tmiw/ezDV/firmware/main/network/icom/CIVState.cpp

/* 
 * This file is part of the ezDV project (https://github.com/tmiw/ezDV).
 * Copyright (c) 2022 Mooneer Salem
 * 
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
 * You should have received a copy of the GNU General Public License 
 * along with this program. If not, see <http://www.gnu.org/licenses/>.
 */

#include <functional>
#include "CIVState.h"
#include "IcomStateMachine.h"
#include "network/ReportingMessage.h"

namespace ezdv
{

namespace network
{

namespace icom
{

CIVState::CIVState(IcomStateMachine* parent)
    : TrackedPacketState(parent)
    , civWatchdogTimer_(parent_->getTask(), this, &CIVState::onCIVWatchdog_, MS_TO_US(WATCHDOG_PERIOD), "IcomCivWatchdog")
    , civSequenceNumber_(0)
    , civId_(0)
    , currentPttState_(false)
{
    parent_->getTask()->registerMessageHandler(this, &CIVState::onFreeDVSetPTTStateMessage_);
    parent_->getTask()->registerMessageHandler(this, &CIVState::onStopTransmitMessage_);
}

void CIVState::onEnterState()
{
    TrackedPacketState::onEnterState();
    
    // Initialize state
    civSequenceNumber_ = 0;
    civId_ = 0;
    
    sendCIVOpenPacket_();
    
    // Send request to get the radio ID on the other side.
    uint8_t civPacket[] = {
        0xFE,
        0xFE,
        0x00,
        0xE0,
        0x19, // Request radio ID command/subcommand
        0x00,
        0xFD
    };

    sendCIVPacket_(civPacket, sizeof(civPacket));
}

void CIVState::onExitState()
{
    civId_ = 0;
    
    civWatchdogTimer_.stop();

    // Send CIV close packet before performing general close processing.
    sendCIVClosePacket_();
    
    TrackedPacketState::onExitState();
}

std::string CIVState::getName()
{
    return "CIV";
}

void CIVState::onReceivePacket(IcomPacket& packet)
{
    uint8_t* civPacket;
    uint16_t civLength;
    
    if (packet.isCivPacket(&civPacket, &civLength))
    {
        civWatchdogTimer_.stop();
        
        ESP_LOGI(parent_->getName().c_str(), "Received CIV packet (from %02x, to %02x, type %02x)", civPacket[3], civPacket[2], civPacket[4]);
        
        // Get the current CI-V address of the radio for future use.
        if (civPacket[2] == 0xE0 && civPacket[4] == 0x19)
        {
            civId_ = civPacket[3];

            // Once we've retrieved the CIV ID, we should retrieve the current frequency
            // for Reporter support.
            uint8_t civPacket[] = {
                0xFE,
                0xFE,
                civId_,
                0xE0,
                0x03, // Request frequency
                0xFD
            };

            sendCIVPacket_(civPacket, sizeof(civPacket));
            
            // We should also reset the PTT state in case we lost connection during a state
            // change.
            ESP_LOGI(parent_->getName().c_str(), "Sending PTT CIV message (PTT = %d)", currentPttState_ ? 1 : 0);
        
            uint8_t civPttPacket[] = {
                0xFE,
                0xFE,
                civId_,
                0xE0,
                0x1C, // PTT on/off command/subcommand
                0x00,
                (uint8_t)(currentPttState_ ? 0x01 : 0x00), // enable PTT
                0xFD
            };
        
            sendCIVPacket_(civPttPacket, sizeof(civPttPacket));
        }
        else if (civPacket[3] == civId_)
        {
            if (civPacket[4] == 0x00 || civPacket[4] == 0x03)
            {
                // Get frequency data for future FreeDV Reporter support -- TBD
                // Frequency data is BCD and starts from index 5.
                uint64_t freqHz = 
                    (civPacket[5] & 0x0F) +                        // 1 Hz
                    ((civPacket[5] & 0xF0) >> 4) * 10           +  // 10 Hz
                    (civPacket[6] & 0x0F) * 100                 +  // 100 Hz
                    ((civPacket[6] & 0xF0) >> 4) * 1000         +  // 1 KHz
                    (civPacket[7] & 0x0F) * 10000               +  // 10 KHz
                    ((civPacket[7] & 0xF0) >> 4) * 100000       +  // 100 KHz
                    (civPacket[8] & 0x0F) * 1000000             +  // 1 MHz
                    ((civPacket[8] & 0xF0) >> 4) * 10000000     +  // 10 MHz
                    (civPacket[9] & 0x0F) * 100000000           +  // 100 MHz
                    ((civPacket[9] & 0xF0) >> 4) * 1000000000;     // 1 GHz

                ESP_LOGI(parent_->getName().c_str(), "Radio frequency changed to %" PRIu64 " Hz", freqHz);

                // Report frequency change to reporters
                ReportFrequencyChangeMessage message(freqHz);
                parent_->getTask()->publish(&message);
            }
        }
    }

    // Call into parent to perform missing packet handling.
    TrackedPacketState::onReceivePacket(packet);
}

void CIVState::onCIVWatchdog_(DVTimer*)
{
    ESP_LOGW(parent_->getName().c_str(), "No CIV data received recently, reconnecting channel");
    parent_->transitionState(IcomProtocolState::ARE_YOU_THERE);
}

void CIVState::sendCIVOpenPacket_()
{
    ESP_LOGI(parent_->getName().c_str(), "Sending CIV open packet");
    auto packet = IcomPacket::CreateCIVOpenClosePacket(civSequenceNumber_++, parent_->getOurIdentifier(), parent_->getTheirIdentifier(), false);
    sendTracked_(packet);
}

void CIVState::sendCIVClosePacket_()
{
    ESP_LOGI(parent_->getName().c_str(), "Sending CIV close packet");
    auto packet = IcomPacket::CreateCIVOpenClosePacket(civSequenceNumber_++, parent_->getOurIdentifier(), parent_->getTheirIdentifier(), true);
    sendTracked_(packet);
}

void CIVState::sendCIVPacket_(uint8_t* civPacket, uint16_t civLength)
{
    ESP_LOGI(parent_->getName().c_str(), "Sending CIV data packet");
    auto packet = IcomPacket::CreateCIVPacket(parent_->getOurIdentifier(), parent_->getTheirIdentifier(), civSequenceNumber_++, civPacket, civLength);
    sendTracked_(packet);
    
    civWatchdogTimer_.stop();
    civWatchdogTimer_.start();
}

void CIVState::onFreeDVSetPTTStateMessage_(DVTask* origin, ezdv::audio::FreeDVSetPTTStateMessage* message)
{
    if (civId_ > 0 && message->pttState)
    {
        // This only handles the beginning of TX. Ending TX is handled by TransmitCompleteMessage.
        ESP_LOGI(parent_->getName().c_str(), "Sending PTT CIV message (PTT = %d)", message->pttState);
        
        uint8_t civPacket[] = {
            0xFE,
            0xFE,
            civId_,
            0xE0,
            0x1C, // PTT on/off command/subcommand
            0x00,
            (uint8_t)0x01, // enable PTT
            0xFD
        };
        
        sendCIVPacket_(civPacket, sizeof(civPacket));
        
        currentPttState_ = true;
    }
}

void CIVState::onStopTransmitMessage_(DVTask* origin, StopTransmitMessage* message)
{
    if (civId_ > 0)
    {
        ESP_LOGI(parent_->getName().c_str(), "Sending PTT CIV message (PTT = %d)", 0);
        
        uint8_t civPacket[] = {
            0xFE,
            0xFE,
            civId_,
            0xE0,
            0x1C, // PTT on/off command/subcommand
            0x00,
            (uint8_t)0x00, // disable PTT
            0xFD
        };
        
        sendCIVPacket_(civPacket, sizeof(civPacket));
        
        currentPttState_ = false;
    }
}

}

}

}
