tmiw/ezDV/firmware/main/driver/TLV320.cpp

/* 
 * This file is part of the ezDV project (https://github.com/tmiw/ezDV).
 * Copyright (c) 2022 Mooneer Salem
 * 
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
 * You should have received a copy of the GNU General Public License 
 * along with this program. If not, see <http://www.gnu.org/licenses/>.
 */

#include <cstring>

#include "esp_log.h"
#include "driver/gpio.h"
#include "driver/i2s_std.h"

#include "TLV320.h"
#include "TLV320Message.h"

// TLV320 reset pin GPIO
#define TLV320_RESET_GPIO GPIO_NUM_13

// TLV320 I2S interface GPIOs
#define TLV320_MCLK_GPIO GPIO_NUM_3
#define TLV320_BCLK_GPIO GPIO_NUM_46
#define TLV320_WCLK_GPIO GPIO_NUM_9
#define TLV320_DIN_GPIO GPIO_NUM_11
#define TLV320_DOUT_GPIO GPIO_NUM_10

// TLV320 I2C address
#define TLV320_I2C_ADDRESS (0x18)

// Tag to prepend to log entries coming from this file.
#define CURRENT_LOG_TAG ("TLV320Driver")

// Timer constants below are for 8000 Hz sample rate
#define I2S_NUM_SAMPLES_PER_INTERVAL (160)

namespace ezdv
{

namespace driver
{

using namespace std::placeholders;

TLV320::TLV320(I2CMaster* i2cMaster)
    : DVTask("TLV320Driver", 15, 4096, tskNO_AFFINITY, 10, pdMS_TO_TICKS(10))
    , audio::AudioInput(2, 2)
    , currentPage_(-1) // This will cause the page to be set to 0 on first I2C write.
    , i2sTxDevice_(nullptr)
    , i2sRxDevice_(nullptr)
    , int1Gpio_(this, std::bind(&TLV320::onInterrupt1Fire_, this, _2), false, true, false)
    , int2Gpio_(this, std::bind(&TLV320::onInterrupt2Fire_, this, _2), false, true, false)
{
    // Register message handlers
    registerMessageHandler<storage::LeftChannelVolumeMessage>(this, &TLV320::onLeftChannelVolume_);
    registerMessageHandler<storage::RightChannelVolumeMessage>(this, &TLV320::onRightChannelVolume_);

    initializeResetGPIO_();
    
    i2cDevice_ = i2cMaster->getDevice(TLV320_I2C_ADDRESS);
    assert(i2cDevice_ != nullptr);
}

TLV320::~TLV320()
{
    delete i2cDevice_;
}

void TLV320::onTaskStart_()
{
    // To begin, we need to hard reset the TLV320.
    ESP_LOGI(CURRENT_LOG_TAG, "reset TLV320");
    initializeResetGPIO_();
    tlv320HardReset_();
    
    // Make sure the TLV320 is actually there. If not, no point in continuing.
    bool result = false;
    getConfigurationOption_(0, 0, &result);
    if (!result)
    {
        ESP_LOGW(CURRENT_LOG_TAG, "Cannot communicate with TLV320, possibly using ezDV on board without one");
        return;
    }
    
    // Initialize I2S.
    initializeI2S_();
    
    // Enable required clocks.
    ESP_LOGI(CURRENT_LOG_TAG, "configure clocks");
    tlv320ConfigureClocks_();
    
    // Configure processing blocks
    ESP_LOGI(CURRENT_LOG_TAG, "configure processing blocks");
    tlv320ConfigureProcessingBlocks_();
    
    ESP_LOGI(CURRENT_LOG_TAG, "configure LDOs");
    tlv320ConfigurePower_();
    
    // Set power and I/O routing (ADC).
    ESP_LOGI(CURRENT_LOG_TAG, "configure routing for ADC");
    tlv320ConfigureRoutingADC_();
    
    // Set power and I/O routing (DAC).
    ESP_LOGI(CURRENT_LOG_TAG, "configure routing for DAC");
    tlv320ConfigureRoutingDAC_();

    // Enable interrupts
    ESP_LOGI(CURRENT_LOG_TAG, "configuring interrupts");
    tlv320ConfigureInterrupts_();

    // Note: restoring AGC volumes is delayed until we get the power-on
    // volumes from storage.
    ESP_LOGI(CURRENT_LOG_TAG, "all audio codec config complete");
}

void TLV320::onTaskSleep_()
{
    // Stop reading from I2S.
    if (i2sRxDevice_ != nullptr)
    {
        i2s_channel_disable(i2sRxDevice_);
        i2s_del_channel(i2sRxDevice_);
    }
    
    if (i2sTxDevice_ != nullptr)
    {
        i2s_channel_disable(i2sTxDevice_);
        i2s_del_channel(i2sTxDevice_);
    }
    
    i2sRxDevice_ = nullptr;
    i2sTxDevice_ = nullptr;

    tlv320HardReset_();
}

void TLV320::onTaskTick_()
{
    if (i2sRxDevice_ == nullptr || i2sTxDevice_ == nullptr) return;

    short tempData[I2S_NUM_SAMPLES_PER_INTERVAL * 2];
    memset(tempData, 0, sizeof(tempData));
    
    // Perform read from I2S. 
    size_t bytesRead = sizeof(tempData);
    ESP_ERROR_CHECK(i2s_channel_read(i2sRxDevice_, tempData, sizeof(tempData), &bytesRead, portMAX_DELAY));

    // Output channel bytes to configured output FIFOs.
    struct FIFO* leftChannelFifo = getAudioOutput(audio::AudioInput::ChannelLabel::LEFT_CHANNEL);
    struct FIFO* rightChannelFifo = getAudioOutput(audio::AudioInput::ChannelLabel::RIGHT_CHANNEL);
    for (int index = 0; index < bytesRead / 2 / sizeof(short); index++)
    {
        if (leftChannelFifo != nullptr) codec2_fifo_write(leftChannelFifo, &tempData[2*index], 1);
        if (rightChannelFifo != nullptr) codec2_fifo_write(rightChannelFifo, &tempData[2*index + 1], 1);
    }

    leftChannelFifo = getAudioInput(audio::AudioInput::ChannelLabel::LEFT_CHANNEL);
    rightChannelFifo = getAudioInput(audio::AudioInput::ChannelLabel::RIGHT_CHANNEL);
    if ((leftChannelFifo && codec2_fifo_used(leftChannelFifo) >= I2S_NUM_SAMPLES_PER_INTERVAL) || 
        (rightChannelFifo && codec2_fifo_used(rightChannelFifo) >= I2S_NUM_SAMPLES_PER_INTERVAL))
    {
        memset(tempData, 0, sizeof(tempData));
        
        for (auto index = 0; index < I2S_NUM_SAMPLES_PER_INTERVAL; index++)
        {
            if (leftChannelFifo) codec2_fifo_read(leftChannelFifo, &tempData[2*index], 1);
            if (rightChannelFifo) codec2_fifo_read(rightChannelFifo, &tempData[2*index + 1], 1);
        }
        
        size_t bytesWritten = 0;
        ESP_ERROR_CHECK(i2s_channel_write(i2sTxDevice_, tempData, sizeof(tempData), &bytesWritten, portMAX_DELAY));
    }
}

void TLV320::setVolumeCommon_(uint8_t reg, int8_t vol)
{
    ESP_LOGI(CURRENT_LOG_TAG, "Volume control: setting volume on register %d to %d", (int)reg, vol);    
    setConfigurationOption_(0, reg, vol);
}

void TLV320::onLeftChannelVolume_(DVTask* origin, storage::LeftChannelVolumeMessage* message)
{
    setVolumeCommon_(65, message->volume);
}

void TLV320::onRightChannelVolume_(DVTask* origin, storage::RightChannelVolumeMessage* message)
{
    setVolumeCommon_(66, message->volume);
}

void TLV320::setPage_(uint8_t page)
{
    uint8_t buf[] = { page };
    i2cDevice_->writeBytes(0, buf, sizeof(buf));
    currentPage_ = page;
}

void TLV320::setConfigurationOption_(uint8_t page, uint8_t reg, uint8_t val)
{
    if (page != currentPage_)
    {
        setPage_(page);
    }
    
    uint8_t buf[] = { val };
    i2cDevice_->writeBytes(reg, buf, sizeof(buf));
}

void TLV320::setConfigurationOptionMultiple_(uint8_t page, uint8_t reg, uint8_t* val, uint8_t size)
{
    if (page != currentPage_)
    {
        setPage_(page);
    }

    i2cDevice_->writeBytes(reg, val, size);
}

uint8_t TLV320::getConfigurationOption_(uint8_t page, uint8_t reg, bool* readResult)
{
    if (page != currentPage_)
    {
        setPage_(page);
    }
    
    uint8_t result[] = { 0 };
    auto rv = i2cDevice_->readBytes(reg, result, sizeof(result));
    if (!rv)
    {
        ESP_LOGE(CURRENT_LOG_TAG, "Could not read bytes from I2C!");
    }
    
    if (readResult != nullptr)
    {
        *readResult = rv;
    }
    
    return result[0];
}

void TLV320::initializeI2S_()
{
    // Get the default channel configuration by helper macro.
    i2s_chan_config_t chan_cfg = I2S_CHANNEL_DEFAULT_CONFIG(I2S_NUM_0, I2S_ROLE_MASTER);

    // Update DMA info for the channel to prevent overflows.
    //chan_cfg.dma_desc_num = 16;
    //chan_cfg.dma_frame_num = I2S_NUM_SAMPLES_PER_INTERVAL;
    chan_cfg.auto_clear = true;
    
    // Allocate a new full duplex channel and get the handles of the channels
    ESP_ERROR_CHECK(i2s_new_channel(&chan_cfg, &i2sTxDevice_, &i2sRxDevice_));

    // Set up configuration for the I2S device:
    //     8 KHz sample rate
    //     Philips format (1 bit shifted, 16 bit/channel stereo)
    //     GPIOs as listed
    i2s_std_config_t i2sConfiguration = {
        .clk_cfg = {
            .sample_rate_hz = 8000,
            .clk_src = I2S_CLK_SRC_DEFAULT,
            .ext_clk_freq_hz = 0, // ignored by ESP-IDF
            .mclk_multiple = I2S_MCLK_MULTIPLE_256,
        },
        .slot_cfg = I2S_STD_PHILIP_SLOT_DEFAULT_CONFIG(I2S_DATA_BIT_WIDTH_16BIT, I2S_SLOT_MODE_STEREO),
        .gpio_cfg = {
            .mclk = TLV320_MCLK_GPIO,
            .bclk = TLV320_BCLK_GPIO,
            .ws = TLV320_WCLK_GPIO,
            .dout = TLV320_DOUT_GPIO,
            .din = TLV320_DIN_GPIO,
            .invert_flags = {
                .mclk_inv = false,
                .bclk_inv = false,
                .ws_inv = false,
            },
        },
    };
    
    // Set clock multiplier to 512 to support increased DAC oversampling ratio
    i2sConfiguration.clk_cfg.mclk_multiple = I2S_MCLK_MULTIPLE_512;

    ESP_ERROR_CHECK(i2s_channel_init_std_mode(i2sTxDevice_, &i2sConfiguration));
    ESP_ERROR_CHECK(i2s_channel_init_std_mode(i2sRxDevice_, &i2sConfiguration));
    ESP_ERROR_CHECK(i2s_channel_enable(i2sTxDevice_));
    ESP_ERROR_CHECK(i2s_channel_enable(i2sRxDevice_));
}

void TLV320::initializeResetGPIO_()
{
    gpio_intr_disable(TLV320_RESET_GPIO);
    gpio_set_direction(TLV320_RESET_GPIO, GPIO_MODE_OUTPUT);
    gpio_set_pull_mode(TLV320_RESET_GPIO, GPIO_FLOATING);
    gpio_set_level(TLV320_RESET_GPIO, 1); // active low
}

void TLV320::tlv320HardReset_()
{
    // TLV320's reset line must be held low for 10ns for the reset
    // to start. We also have to wait for 1ms after the reset
    // goes high for everything to reset properly. See section 3.1-3.2 
    // of the Application Reference Guide 
    // (https://www.ti.com/lit/an/slaa408a/slaa408a.pdf).
    gpio_set_level(TLV320_RESET_GPIO, 0);
    esp_rom_delay_us(1);
    gpio_set_level(TLV320_RESET_GPIO, 1);
    vTaskDelay(pdMS_TO_TICKS(1));
}

void TLV320::tlv320ConfigureClocks_()
{
    // Clock calculations for 8K sample rate per guide at 
    // https://www.ti.com/lit/an/slaa404c/slaa404c.pdf
            
    // AOSR = 128
    // DOSR = 768
    // ADC_FS = 8K
    // DAC_FS = 8K
    // ADC_MOD_CLK = AOSR * ADC_FS = 128 * 8000 = 1.024 MHz <= 6.758 MHz
    // DAC_MOD_CLK = DOSR * DAC_FS = 768 * 8000 = 6.144 MHz <= 6.758 MHz
    
    // ADC Processing Block = PRB_R1
    // DAC Processing Block = PRB_P1
    // MADC = 48
    // MDAC = 8
    // ADC_CLK = MADC * ADC_MOD_CLK = 48 * 1.024 MHz = 49.152 MHz
    // DAC_CLK = MDAC * DAC_MOD_CLK = 8 * 6.144 MHz = 49.152 MHz
    // (MADC * AOSR) / 32 = 6144 / 32 = 192 >= RC(R1) = 6
    // (MDAC * DOSR) / 32 = 6144 / 32 = 192 >= RC(P1) = 8
    // ADC_CLK <= 55.296 MHz
    // DAC_CLK <= 55.296 MHz
    
    // NADC = 2
    // NDAC = 2
    // CODEC_CLKIN = NADC * ADC_CLK = NDAC * DAC_CLK = 98.304 MHz
    // CODEC_CLKIN <= 137MHz
    // CODEC_CLKIN from PLL_CLK
    
    // PLL_CLK = MCLK * R * J.D/P
    // 98.304 MHz = 4.096 * 1 * 24.0000 / 1
    // P = 1, R = 1, J = 24, D = 0 

    uint8_t pllOpts[] = {
        // Set CODEC_CLKIN to PLL and use MCLK for PLL
        // (Page 0, register 4)
        (0 << 2) | 0b11,

        // Set PLL P = 1, R = 1, J = 24, D = 0, power up PLL
        // (Page 0, registers 5-8)
        (1 << 7) | (0b001 << 4) | (0b001),  // P, R, power up
        24, // J
        0, // D[MSB]
        0 // D[LSB]
    };
    setConfigurationOptionMultiple_(0, 4, pllOpts, 5);

    // Wait 10ms for PLL to become available
    // (Section 2.7.1, "TLV320AIC3254 Application Reference Guide")
    vTaskDelay(pdMS_TO_TICKS(10));
        
    // Set NDAC = 2, MDAC = 8. Power on divider.
    // (Page 0, registers 11 and 12)
    // Program DOSR to 768 (Page 0, registers 13-14)
    uint8_t dacOpts[] = {
        (1 << 7) | 2,
        (1 << 7) | 8,
        0b11,
        0
    };
    setConfigurationOptionMultiple_(0, 11, dacOpts, 4);
        
    // Set NADC = 2, MADC = 48. (Page 0, registers 18 and 19)
    // Program AOSR to 128 (Page 0, register 20).
    uint8_t adcOpts[] = {
        2,
        (1 << 7) | 48,
        128
    };
    setConfigurationOptionMultiple_(0, 18, adcOpts, 2);
    
    // Set I2S word size to 16 bits (Page 0, register 27)
    setConfigurationOption_(0, 27, 0);
    
#if 0
    // Loopback audio at the ADC/DAC level
    setConfigurationOption_(0, 29, 1 << 4);
#endif // 0
}

void TLV320::tlv320ConfigurePower_()
{
    // Power up AVDD LDO
    setConfigurationOption_(1, 2, (1 << 3) | (1 << 0));
    
    // Disable weak AVDD in presence of external AVDD supply (Page 1, register 1)
    setConfigurationOption_(1, 1, (1 << 3));
    
    // AVDD/DVDD 1.72V, AVDD LDO powered up (Page 1, register 2)
    setConfigurationOption_(1, 2, (0 << 3) | (1 << 0));
    
    // Set full chip common mode to 0.9V
    // HP output CM = 1.65V
    // HP driver supply = LDOin voltage
    // Line output CM = 1.65V
    // Line output supply = LDOin voltage
    // (Page 1, register 10)
    setConfigurationOption_(1, 10, (3 << 4) | (1 << 3) | (1 << 1) | (1 << 0));
    
    // Set ADC PTM to PTM_R1 (Page 1, register 61)
    setConfigurationOption_(1, 61, 0xFF);
    
    // Set DAC PTM to PTM_P1 (Page 1, registers 3-4)
    // Note: PTM_P4 requires >= 20 bits for I2S, hence not used here.
    uint8_t dacPtm[] = {
        0x2 << 2,
        0x2 << 2
    };
    setConfigurationOptionMultiple_(1, 3, dacPtm, 2);
    
    // Set input powerup time to 3.1ms (Page 1, register 71)
    setConfigurationOption_(1, 71, 0b110001);
    
    // REF will power up in 40ms (Page 1, register 123)
    setConfigurationOption_(1, 123, 1);
}

void TLV320::tlv320ConfigureProcessingBlocks_()
{
    // Set ADC_PRB and DAC_PRB to P1 and R1 (Page 0, registers 60-61).
    // Note: Use ADC_PRB = R2 if enabling the ADC filter below.
    uint8_t prb[] = {
        1,
        1
    };
    setConfigurationOptionMultiple_(0, 60, prb, 2);
    
    // Set ADC filter coefficients for HPF, center frequency 130 Hz.
    // All five biquads on both channels are set to this filter to reduce
    // background hiss in the recorded audio.
    uint8_t adcFilter[] = {
        0x77, 0x15, 0x39, 0x00,
        0x88, 0xEA, 0xC7, 0x00,
        0x77, 0x15, 0x39, 0x00,
        0x76, 0xC5, 0xA2, 0x00,
        0x91, 0x36, 0x60, 0x00
    };
    setConfigurationOptionMultiple_(8, 36, adcFilter, sizeof(adcFilter));
    setConfigurationOptionMultiple_(9, 44, adcFilter, sizeof(adcFilter));
    setConfigurationOptionMultiple_(8, 56, adcFilter, sizeof(adcFilter));
    setConfigurationOptionMultiple_(9, 64, adcFilter, sizeof(adcFilter));
    setConfigurationOptionMultiple_(8, 76, adcFilter, sizeof(adcFilter));
    setConfigurationOptionMultiple_(9, 84, adcFilter, sizeof(adcFilter));
    setConfigurationOptionMultiple_(8, 96, adcFilter, sizeof(adcFilter));
    setConfigurationOptionMultiple_(9, 104, adcFilter, sizeof(adcFilter));
    setConfigurationOptionMultiple_(8, 116, adcFilter, sizeof(adcFilter));
    setConfigurationOptionMultiple_(9, 124, adcFilter, sizeof(adcFilter));
}

void TLV320::tlv320ConfigureRoutingADC_()
{
    // Enable 2.5V mic bias on headset jack using LDOIN (Page 1, register 51)
    setConfigurationOption_(1, 51, (1 << 6) | (0b10 << 4) | (1 << 3));
    
    // Set ADC routing: IN1_L left channel, IN1_R right channel,
    // 20kohm impedence (Page 1, registers 52, 54, 55, 57)
    setConfigurationOption_(1, 52, 0b10 << 6);
    setConfigurationOption_(1, 54, 0b10 << 6);
    setConfigurationOption_(1, 55, 0b10 << 6);
    setConfigurationOption_(1, 57, 0b10 << 6);
    
    // Weakly connect all unused inputs to ground.
    // (Page 1, register 58)
    setConfigurationOption_(1, 58, (1 << 5) | (1 << 4) | (1 << 3) | (1 << 2));
    
    // Unmute PGAs, gain = 6dB due to 20k impedence
    // (Page 1, registers 59 and 60)
    setConfigurationOption_(1, 59, 0x0c);
    setConfigurationOption_(1, 60, 0x0c);
    
    // Power on ADC (Page 0, register 81)
    setConfigurationOption_(0, 81, (1 << 7) | (1 << 6));
    
    // Unmute ADC (Page 0, register 82)
    setConfigurationOption_(0, 82, 0);
    
    //setConfigurationOption_(0, 84, 0b0101000 /*0x0c*/);
    
    tlv320ConfigureAGC_();
}

void TLV320::tlv320ConfigureRoutingDAC_()
{
    // 6kohm depop, N = 6.0 (Page 1, register 20)
    setConfigurationOption_(1, 20, (0b1010 << 2) | (0b01 << 0));
    
    // Set DAC routing: HPL, HPR come from DAC
    // (Page 1, registers 12 and 13)
    setConfigurationOption_(1, 12, 1 << 3);
    setConfigurationOption_(1, 13, 1 << 3);
    
    // Unmute HPL and HPR, gain = 0dB
    // (Page 1, registers 16 and 17)
    setConfigurationOption_(1, 16, 0);
    setConfigurationOption_(1, 17, 0);

    // Power up HPL and HPR
    // (Page 1, register 9)
    setConfigurationOption_(1, 9, (1 << 5) | (1 << 4));
    
    // Wait until gain fully applied. This effectively takes ~2.5s
    // to complete unless the TLV320 gets back to us sooner.
    // (Page 1, register 63)
    uint8_t gainRegVal = 0;
    int count = 0;
    do
    {
        vTaskDelay(pdMS_TO_TICKS(10));
        gainRegVal = getConfigurationOption_(1, 63);
    } while ((count++ <= 250) && (gainRegVal & (0b11 << 6)) == 0);

    if (count > 250)
    {
        ESP_LOGW(CURRENT_LOG_TAG, "Timed out waiting for gain to fully apply, assuming it's already taken effect");
    }
    
    // Power on DAC (Page 0, register 63)
    setConfigurationOption_(0, 63, (1 << 7) | (1 << 6) | (1 << 4) | (1 << 2) | (1 << 1));
    
    // Unmute DAC (Page 0, register 64)
    setConfigurationOption_(0, 64, 0);
}

void TLV320::tlv320ConfigureAGC_()
{
    uint8_t agcConfig[] = {
        // Enable AGC, -16dB target, gain hysteresis disabled
        (1 << 7) | (0b101 << 4) | (0b00 << 0),  
        
        // Hysteresis 2dB, -90dB noise threshold
        (0b01 << 6) | (0b11111 << 1),
        
        // 40dB maximum gain
        0x50, //0b100100,
        
        // Attack time = 20ms (25 * 32 clocks, scale 2)
        0x08,
        
        // Decay time = 500ms (19 * 512 clocks, scale 2)
        0x32,
        
        // Noise debounce = 0ms
        0x00,
        
        // Signal debounce = 2ms
        0x06,
    };
    
    // Set AGC configuration for both channels (page 0, register 86 for left, register 94 for right)
    setConfigurationOptionMultiple_(0, 86, agcConfig, sizeof(agcConfig));
    setConfigurationOptionMultiple_(0, 94, agcConfig, sizeof(agcConfig));
}

void TLV320::tlv320ConfigureInterrupts_()
{
    // Set headphone overcurrent detection debounce to 128ms
    // (Page 1, Register 11, Bit D4 = 1, D3-1 = 101)
    setConfigurationOption_(1, 11, (1 << 4) | (0b101 << 1));
    
    // Use INT1 for ADC/DAC overload event
    // (Page 0, Register 48, Bit D2 = 1)

    // Use INT2 for button press, headset detect event
    // (Page 0, Register 49, Bit D6 = 1)

    uint8_t interruptConfig[] = 
    {
        (1 << 2) | (1 << 0),
        (1 << 7) | (1 << 6) | (1 << 0)
    };
    setConfigurationOptionMultiple_(0, 48, interruptConfig, sizeof(interruptConfig));

    // Disable SCLK so we can use it for headset detection
    // (Page 0, Register 56, D2-D1 = 00)
    setConfigurationOption_(0, 56, 0b00 << 1);

    // Enable headset detection (required for button detection) with 32ms debounce.
    // (Page 0, Register 67, D7 = 1)
    setConfigurationOption_(0, 67, (1 << 7) | (0b11 << 0));

    // INT1 output on MFP4
    // (Page 0, Register 55, Bits D4-D1 = 0100)
    setConfigurationOption_(0, 55, 0b0100 << 1);

    // INT2 output on MFP5
    // (Page 0, Register 52, Bits D5-D2 = 0110)
    setConfigurationOption_(0, 52, 0b0110 << 2);

    // Enable interrupts
    int1Gpio_.start();
    int1Gpio_.enableInterrupt(true);
    int2Gpio_.start();
    int2Gpio_.enableInterrupt(true);
}

void TLV320::onInterrupt1Fire_(bool state)
{
    // Page 0, register 42, bits D3-D2 contain the ADC channels that
    // overloaded.
    auto val = getConfigurationOption_(0, 42);
    bool leftAdcOverload = val & (1 << 3);
    bool rightAdcOverload = val & (1 << 2);

    if (state && (leftAdcOverload || rightAdcOverload))
    {
        ESP_LOGW(CURRENT_LOG_TAG, "ADC overload! (Left/User = %d, Right/Radio = %d)", leftAdcOverload, rightAdcOverload);

        // Broadcast current ADC status to interested parties.
        OverloadStateMessage message(leftAdcOverload, rightAdcOverload);
        publish(&message);
    }
    else
    {
        // Broadcast "clear" ADC message so that any indication (LED, etc.)
        // doesn't remain.
        OverloadStateMessage message(false, false);
        publish(&message);
    }
}

void TLV320::onInterrupt2Fire_(bool state)
{   
    if (state)
    {
        // Page 0, register 44, bit D5 contains the status of the headset button
        auto val = getConfigurationOption_(0, 44);
        ESP_LOGI(CURRENT_LOG_TAG, "button state: %x", val);
        if (val & (1 << 5))
        {
            ESP_LOGI(CURRENT_LOG_TAG, "Headset button pressed");

            HeadsetButtonPressMessage message;
            publish(&message);
        }
    }
}

} // namespace driver

} // namespace ezdv
