tmiw/ezDV/firmware/main/driver/ButtonArray.cpp

/* 
 * This file is part of the ezDV project (https://github.com/tmiw/ezDV).
 * Copyright (c) 2022 Mooneer Salem
 * 
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
 * You should have received a copy of the GNU General Public License 
 * along with this program. If not, see <http://www.gnu.org/licenses/>.
 */

#include "esp_log.h"

#include "ButtonArray.h"
#include "InputGPIO.h"

// One second for long press
#define LONG_PRESS_INTERVAL_US (1000000)

namespace ezdv
{

namespace driver
{

using namespace std::placeholders;

ButtonArray::ButtonArray()
    : DVTask("ButtonArray", 10, 3072, tskNO_AFFINITY, 10)
    , pttButtonTimer_(this, std::bind(&ButtonArray::handleLongPressButton_, this, ButtonLabel::PTT), LONG_PRESS_INTERVAL_US, "PttButtonTimer")
    , modeButtonTimer_(this, std::bind(&ButtonArray::handleLongPressButton_, this, ButtonLabel::MODE), LONG_PRESS_INTERVAL_US, "ModeButtonTimer")
    , volUpButtonTimer_(this, std::bind(&ButtonArray::handleLongPressButton_, this, ButtonLabel::VOL_UP), LONG_PRESS_INTERVAL_US, "VolUpTimer")
    , volDownButtonTimer_(this, std::bind(&ButtonArray::handleLongPressButton_, this, ButtonLabel::VOL_DOWN), LONG_PRESS_INTERVAL_US, "VolDownTimer")
    , pttButton_(this, std::bind(&ButtonArray::handleButton_, this, ButtonLabel::PTT, _2))
    , modeButton_(this, std::bind(&ButtonArray::handleButton_, this, ButtonLabel::MODE, _2))
    , volUpButton_(this, std::bind(&ButtonArray::handleButton_, this, ButtonLabel::VOL_UP, _2))
    , volDownButton_(this, std::bind(&ButtonArray::handleButton_, this, ButtonLabel::VOL_DOWN, _2))
{
    // empty
}

ButtonArray::~ButtonArray()
{
    // empty
}

void ButtonArray::onTaskStart_()
{
    pttButton_.start();
    pttButton_.enableInterrupt(true);
    
    modeButton_.start();
    modeButton_.enableInterrupt(true);
    
    volUpButton_.start();
    volUpButton_.enableInterrupt(true);
    
    volDownButton_.start();
    volDownButton_.enableInterrupt(true);
}

void ButtonArray::onTaskSleep_()
{
    pttButton_.enableInterrupt(false);
    modeButton_.enableInterrupt(false);
    volUpButton_.enableInterrupt(false);
    volDownButton_.enableInterrupt(false);
}

static const char* ButtonLabelStrings_[] = {
    "None",
    "PTT",
    "Mode",
    "VolUp",
    "VolDown"
};

void ButtonArray::handleButton_(ButtonLabel label, bool val)
{
    DVTimer* timerToSet = nullptr;
    bool buttonPressed = !val;

    switch(label)
    {
        case ButtonLabel::PTT:
            timerToSet = &pttButtonTimer_;
            break;
        case ButtonLabel::MODE:
            timerToSet = &modeButtonTimer_;
            break;
        case ButtonLabel::VOL_UP:
            timerToSet = &volUpButtonTimer_;
            break;
        case ButtonLabel::VOL_DOWN:
            timerToSet = &volDownButtonTimer_;
            break;
        default:
            assert(0);
    }

    ESP_LOGI("ButtonArray", "Button %s now %d", ButtonLabelStrings_[label], (int)buttonPressed);

    // Start long press timer
    if (buttonPressed)
    {
        ButtonShortPressedMessage* message = new ButtonShortPressedMessage(label);
        publish(message);
        delete message;

        if (timerToSet != nullptr)
        {
            timerToSet->stop();
            timerToSet->start(true);
        }
    }
    else
    {
        if (timerToSet != nullptr)
        {
            timerToSet->stop();
        }
        
        ButtonReleasedMessage* message = new ButtonReleasedMessage(label);
        publish(message);
        delete message;
    }
}

void ButtonArray::handleLongPressButton_(ButtonLabel label)
{
    ESP_LOGI("ButtonArray", "Button %s long pressed", ButtonLabelStrings_[label]);

    ButtonLongPressedMessage* message = new ButtonLongPressedMessage(label);
    publish(message);
    delete message;
}

}

}
