tmiw/ezDV/firmware/main/network/icom/IcomMessage.h

/* 
 * This file is part of the ezDV project (https://github.com/tmiw/ezDV).
 * Copyright (c) 2022 Mooneer Salem
 * 
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
 * You should have received a copy of the GNU General Public License 
 * along with this program. If not, see <http://www.gnu.org/licenses/>.
 */

#ifndef ICOM_MESSAGE_H
#define ICOM_MESSAGE_H

#include <cstring>
#include "task/DVTaskMessage.h"
#include "esp_timer.h"

extern "C"
{
    DV_EVENT_DECLARE_BASE(ICOM_MESSAGE);
}

namespace ezdv
{

namespace network
{

namespace icom
{

using namespace ezdv::task;

class IcomPacket;

enum IcomMessageTypes
{
    CIV_AUDIO_CONN_INFO = 1,
    CONNECT_RADIO = 2,
    DISCONNECTED_RADIO = 3,
    SEND_PACKET = 4,
    RECEIVE_PACKET = 5,
    CLOSE_SOCKET = 6,
    STOP_TRANSMIT = 7,
};

class IcomCIVAudioConnectionInfo : public DVTaskMessageBase<CIV_AUDIO_CONN_INFO, IcomCIVAudioConnectionInfo>
{
public:
    IcomCIVAudioConnectionInfo(
        int localCivPortProvided = 0, 
        int remoteCivPortProvided = 0, 
        int localAudioPortProvided = 0, 
        int remoteAudioPortProvided = 0)
        : DVTaskMessageBase<CIV_AUDIO_CONN_INFO, IcomCIVAudioConnectionInfo>(ICOM_MESSAGE)
        , localCivPort(localCivPortProvided)
        , remoteCivPort(remoteCivPortProvided)
        , localAudioPort(localAudioPortProvided)
        , remoteAudioPort(remoteAudioPortProvided)
        {}
    virtual ~IcomCIVAudioConnectionInfo() = default;

    int localCivPort;
    int remoteCivPort;
    int localAudioPort;
    int remoteAudioPort; 
};

class IcomConnectRadioMessage : public DVTaskMessageBase<CONNECT_RADIO, IcomConnectRadioMessage>
{
public:
    static const int STR_SIZE = 32;
    
    IcomConnectRadioMessage(
        const char* ipProvided = nullptr,
        int portProvided = 0,
        const char* usernameProvided = nullptr,
        const char* passwordProvided = nullptr)
        : DVTaskMessageBase<CONNECT_RADIO, IcomConnectRadioMessage>(ICOM_MESSAGE)
        , port(portProvided)
    {
        memset(ip, 0, STR_SIZE);
        memset(username, 0, STR_SIZE);
        memset(password, 0, STR_SIZE);
        
        if (ipProvided != nullptr)
        {
            strncpy(ip, ipProvided, STR_SIZE - 1);
        }
        
        if (usernameProvided != nullptr)
        {
            strncpy(username, usernameProvided, STR_SIZE - 1);
        }
        
        if (passwordProvided != nullptr)
        {
            strncpy(password, passwordProvided, STR_SIZE - 1);
        }
        
        ip[STR_SIZE - 1] = 0;
        username[STR_SIZE - 1] = 0;
        password[STR_SIZE - 1] = 0;
    }
    virtual ~IcomConnectRadioMessage() = default;

    char ip[STR_SIZE];
    int port;
    char username[STR_SIZE];
    char password[STR_SIZE];
};

class DisconnectedRadioMessage : public DVTaskMessageBase<DISCONNECTED_RADIO, DisconnectedRadioMessage>
{
public:
    DisconnectedRadioMessage()
        : DVTaskMessageBase<DISCONNECTED_RADIO, DisconnectedRadioMessage>(ICOM_MESSAGE)
        {}
    virtual ~DisconnectedRadioMessage() = default;
};

class SendPacketMessage : public DVTaskMessageBase<SEND_PACKET, SendPacketMessage>
{
public:
    SendPacketMessage(IcomPacket* packetProvided = nullptr)
        : DVTaskMessageBase<SEND_PACKET, SendPacketMessage>(ICOM_MESSAGE)
        , packet(packetProvided)
        , sendTime(esp_timer_get_time())
        {}
    virtual ~SendPacketMessage() = default;

    IcomPacket* packet;
    int64_t sendTime;
};

class ReceivePacketMessage : public DVTaskMessageBase<RECEIVE_PACKET, ReceivePacketMessage>
{
public:
    ReceivePacketMessage(IcomPacket* packetProvided = nullptr)
        : DVTaskMessageBase<RECEIVE_PACKET, ReceivePacketMessage>(ICOM_MESSAGE)
        , packet(packetProvided)
        {}
    virtual ~ReceivePacketMessage() = default;

    IcomPacket* packet;
};

class CloseSocketMessage : public DVTaskMessageBase<CLOSE_SOCKET, CloseSocketMessage>
{
public:
    CloseSocketMessage()
        : DVTaskMessageBase<CLOSE_SOCKET, CloseSocketMessage>(ICOM_MESSAGE)
        {}
    virtual ~CloseSocketMessage() = default;
};

class StopTransmitMessage : public DVTaskMessageBase<STOP_TRANSMIT, StopTransmitMessage>
{
public:
    StopTransmitMessage()
        : DVTaskMessageBase<STOP_TRANSMIT, StopTransmitMessage>(ICOM_MESSAGE)
        {}
    virtual ~StopTransmitMessage() = default;
};

}

}

}

#endif // ICOM_MESSAGE_H
